ptabor/ledStrip/arduino/ledStripDriver/visualizations.cpp

#include "visualizations.h"
#include "wavelength.h"
#include <Arduino.h>
#include <map>
#include "math.h"

#define MSGEQ_BAND_NO 7

// ===============================================================================

// uint32_t losowyKolorSwiateczny() {
//   uint32_t kolory[] = { 0xFF7521, 0xFFD700, 0xFF4500, /*0x32CD32*/ 0x006400, 0x808000, 0x4682B4, 0x8B4513, 0x800000};

//   //{ 0xff0000, 0x00ff00, 0x0000ff, 0xffffff, 0xffa500};
//   return kolory[rand()%kolory_len];
// }

void lampki(led_channel_t *channel, int t_ms, int prev_t_ms, uint32_t kolory[], int kolory_len) {
  uint32_t *strip=channel->rgbs;
  
  if (prev_t_ms == 0 || (t_ms - prev_t_ms > 1000)) {
    for (int i = 0; i < channel->length; ++i) {
      if (rand()%5 == 0) {
        strip[i] = kolory[rand()%kolory_len];  
      } else {
        strip[i] = 0x000000;
      }
    }
  }

  if (t_ms / 1000 != prev_t_ms / 1000) {
    // Turn off random;
    while(true) {
      uint32_t l = rand()%channel->length;
      if (strip[l] != 0x000000) {
        strip[l] = 0x000000;  
        break; 
      }
    }

    // Turn on random;
    while(true) {
      uint32_t l = rand()%channel->length;
      if (strip[l] == 0x000000) {
       strip[l] = kolory[rand()%kolory_len];
        break; 
      }
    }    
  }
  drawMap(channel, strip);
}

void lampki(led_channel_t *channel, int t_ms, int prev_t_ms) {
  uint32_t kolory[] = { 0xFF4500, /*0xFFD7000xDAA520,*/ 0xFF4500, /*0x32CD32*/ 0x006400, 0x808000, /*0x4682B4*/0x191970, 0x8B4513, 0x800000};
  int kolory_len=7;

  lampki(channel, t_ms, prev_t_ms, kolory, kolory_len);
}


// ============================================================================

void stroboSimple(led_channel_t* channel, int bandValues[MSGEQ_BAND_NO]) {
  uint32_t *strip=channel->rgbs;

  for (int i = 0; i < channel->length; ++i) {
    strip[i] = 0x000000;
  }

  int ledsPerBand = channel->length / MSGEQ_BAND_NO;

  for (int b=0; b<MSGEQ_BAND_NO; ++b) {
    for (int i=0; i < bandValues[b] * ledsPerBand / 100; ++i) {
      strip[b*ledsPerBand + i] = RGB_RED;
    }
  }
  drawMap(channel, strip);
}

// ============================================================================

typedef struct snakeType {
//   steps_per_ms, can be negative to change direction.
  float speed;  
  uint32_t length;
  uint32_t maxLength;
} snakeType;

void clean(led_channel_t *channel) {
  uint32_t *strip=channel->rgbs;
  for (int i = 0; i < channel->length; ++i) {
    strip[i] = 0x000000;
  }
}

uint32_t rainbowRGB(float f) {
  return waveLengthToRGB(380+round(400 * f));
}

void rainbow(led_channel_t *channel, uint32_t t_ms) {
  uint32_t *strip=channel->rgbs;
  for (uint32_t i = 0; i < channel->length; i++) {
    strip[i] = rainbowRGB(pow((float)(channel->length - i - 1) / channel->length, pow(7, sin(t_ms / 5000.0)))); 
  }
  drawMap(channel, strip);
}

void rainbowSnakes(led_channel_t *channel, uint32_t t_ms, struct snakeType snakes[], int numSnakes) {
  uint32_t *strip=channel->rgbs;
  clean(channel);
  for (int s = 0; s < numSnakes; ++s) {
    if (snakes[s].length > 0 && snakes[s].maxLength > 0) {
      for (uint32_t i = 0; i < snakes[s].length; i++) {
        strip[uint32_t(round(snakes[s].speed * t_ms + i + (s * channel->length / numSnakes) )) % channel->length ] = rainbowRGB((float)i / (snakes[s].maxLength - 1));
      }
    }
  }

  drawMap(channel, strip);
}

void rainbowSnakesStrobo(led_channel_t *channel, uint32_t t_ms, int bandValues[MSGEQ_BAND_NO]) {
  struct snakeType snakesArray[MSGEQ_BAND_NO];// = {snakeType1, snakeType2, snakeType3};
  for (int i = 0; i < MSGEQ_BAND_NO; ++i) {
    snakesArray[i].speed=-0.01;
    snakesArray[i].maxLength=channel->length / MSGEQ_BAND_NO;
    snakesArray[i].length=(bandValues[i]/100.0)*snakesArray[i].maxLength;
  }
  rainbowSnakes(channel, t_ms, snakesArray, MSGEQ_BAND_NO);
}

struct snakeType snakeType1 = {0.04, 50, 50};
struct snakeType snakeType2 = {-0.05, 80, 80};
struct snakeType snakeType3 = {0.01, 140, 140};
struct snakeType snakesArray[3] = {snakeType1, snakeType2, snakeType3};

void rainbowSnakesDemo(led_channel_t *channel, uint32_t t_ms) {
  rainbowSnakes(channel, t_ms, snakesArray, 3);
}

void oneByOne(led_channel_t *channel, int t_ms, int per_one_ms) {
  uint32_t *strip=channel->rgbs;
  clean(channel);
  int led = (t_ms / per_one_ms) % channel->length;
  strip[led]= 0xffffff;
  drawMap(channel, strip);
  Serial.printf("Led: ");
  Serial.printf(String(led).c_str());
  Serial.printf("\n");
}

void blyskawicaI(led_channel_t *channel, int t_ms){
  uint32_t *strip=channel->rgbs;
  for (int l = 0; l < 125; ++l) {
    strip[l] |= (130+int(sin(t_ms/300.0 + l/100.0)*120.0)) << 16;
  }
}


void choinkaI(led_channel_t *channel, int t_ms){
  uint32_t *strip=channel->rgbs;
  for (int l = 0; l < 61; ++l) {
    strip[l]|=RGB_GREEN;
  }
  for (int l = 125; l < 237; ++l) {
    strip[l]|=RGB_GREEN;
  }
}


void blyskawica(led_channel_t *channel, int t_ms){
  clean(channel);
  blyskawicaI(channel, t_ms);
  drawMap(channel, channel->rgbs);
}


void choinka(led_channel_t *channel, int t_ms){
  clean(channel);
  choinkaI(channel, t_ms);
  drawMap(channel, channel->rgbs);
}

void choinkaBlyskawica(led_channel_t *channel, int t_ms) {
  clean(channel);
  blyskawicaI(channel, t_ms);
  choinkaI(channel, t_ms);
  drawMap(channel, channel->rgbs);  
}

void grzesia(led_channel_t *channel, int t_ms) {
  uint32_t *strip=channel->rgbs;
  for (int l = 0; l < channel->length; ++l) {
    if ((l+(t_ms/100))%3==0) {
      strip[l]=0xC9A9A6; 
    }
    if ((l+(t_ms/100))%3==1) {
      strip[l]=RGB_GREEN;
    }
    if ((l+(t_ms/100))%3==2) {
      strip[l]=RGB_BLUE;        
    }
  }
  drawMap(channel, strip);  
}

void prefix(led_channel_t *channel, int n, uint32_t color) {
  uint32_t *strip=channel->rgbs;
  for (int l = 0; l < channel->length; ++l) {
    strip[l] = l<n ? color : 0;
    // if ((l+(t_ms/100))%3==0) {
    //   strip[l]=RGB_RED;
    // }
    // if ((l+(t_ms/100))%3==1) {
    //   strip[l]=RGB_GREEN;
    // }
    // if ((l+(t_ms/100))%3==2) {
    //   strip[l]=RGB_BLUE;        
    // }
  }
  drawMap(channel, strip);  
}

void pulses(led_channel_t *channel, int t_ms, uint32_t color) {
  float brightness=abs(sin(t_ms/3000.0));
  Serial.print("snow brightness: ");
  Serial.println(brightness);
  drawColor(channel, applyBrightness(color, brightness)); 
}

void snow(led_channel_t *channel, int t_ms, uint32_t color) {
  uint32_t colors[] = {color};
  snow(channel, t_ms, colors, 1);
}

  typedef struct TStar {
    int age;
    uint32_t color;

    void inc() {age++;};
  } TStar;

void snow(led_channel_t *channel, int t_ms, uint32_t kolory[], int kolory_len) {  
  static std::map<int, TStar> stars;
  static int priv_t_ms=0;
  uint32_t *strip=channel->rgbs;

  for (int i=0; i<channel->length; ++i) {
    strip[i]=0;
  }
  for (auto &s : stars) {
    s.second.inc();
    strip[s.first] = applyBrightness(s.second.color, max(0.2, abs(sin(s.second.age/20.0))));
  }

  if (stars.size()==0) {
    for (int i=0; i < 200; ++i) {
      stars[rand()%channel->length]={.age=rand()%10000, .color=kolory[rand()%kolory_len]};
    }    
  }

  if (priv_t_ms / 2000 != t_ms / 2000) {
    stars[rand()%channel->length]={.age=0, .color=kolory[rand()%kolory_len]};
  }

  if (stars.size() > 250) {
    std::map<int, TStar>::iterator it = stars.begin();
    std::advance(it, rand()%stars.size());
    stars.erase(it);    
  }

  // float brightness=abs(sin(t_ms/3000.0));
  // Serial.print("snow brightness: ");
  // Serial.println(brightness);
  // drawColor(channel, applyBrightness(color, brightness)); 
  priv_t_ms= t_ms;
  drawMap(channel, strip); 
}

void strips(led_channel_t *channel, int t_ms, int speed, uint32_t kolory[], int kolory_len) {
  clean(channel);
  //uint32_t *strip=channel->rgbs;
  for (int l = 0; l < channel->length; ++l) {
    channel->rgbs[l] = kolory[min( (l+t_ms/speed)%channel->length / (channel->length / kolory_len),kolory_len - 1)];
  }
  drawMap(channel, channel->rgbs);
}

void snowIncremental(led_channel_t *channel, int t_ms) {
  static int next_ms=0;
  if (t_ms >= next_ms) {
    uint32_t c=0x000000;
    switch (rand()%5) {
      case 0: 
      case 1: 
        c=0xFFFFFF;
        break;
      case 2: 
        c=0x24B6E9;
        break;
    }
    channel->rgbs[rand()%channel->length] = c;
    next_ms = t_ms+0;//+ rand()%1;  
    drawMap(channel, channel->rgbs);
  }
}
